Jonysand/Reflection/demo/fastLEDdemo/fastLEDdemo.ino

#include <noise.h>
#include <bitswap.h>
#include <fastspi_types.h>
#include <pixelset.h>
#include <fastled_progmem.h>
#include <led_sysdefs.h>
#include <hsv2rgb.h>
#include <fastled_delay.h>
#include <colorpalettes.h>
#include <color.h>
#include <fastspi_ref.h>
#include <fastspi_bitbang.h>
#include <controller.h>
#include <fastled_config.h>
#include <colorutils.h>
#include <chipsets.h>
#include <pixeltypes.h>
#include <fastspi_dma.h>
#include <fastpin.h>
#include <fastspi_nop.h>
#include <platforms.h>
#include <lib8tion.h>
#include <cpp_compat.h>
#include <fastspi.h>
#include <FastLED.h>
#include <dmx.h>
#include <power_mgt.h>

#define NUM_LEDS 84

CRGB leds[NUM_LEDS];
void setup() {
  FastLED.addLeds<NEOPIXEL, 6>(leds, NUM_LEDS); 
}

void loop() {
  leds[0] = CRGB::White; FastLED.show(); delay(30);
  leds[0] = CRGB::Black; FastLED.show(); delay(30);
}
